solarcaratuva/Batterytester/Firmware/Discharge/Discharge/Discharger.cpp

#include "Discharger.h"
Discharger::Discharger(int MYSELPIN,int MYDATAOUT,int MYDATAIN,int MYSPICLOCK){
	SELPIN = MYSELPIN;
	DATAOUT = MYDATAOUT;
	DATAIN = MYDATAIN;
	SPICLOCK = MYSPICLOCK;	
}

int Discharger::read_adc(int channel){
  int adcvalue = 0;
  byte commandbits = B11000000; //command bits - start, mode, chn (3), dont care (3)
  //allow channel selection
  commandbits|=((channel-1)<<3);
  digitalWrite(SELPIN,LOW); //Select adc
  // setup bits to be written
  for (int i=7; i>=3; i--){
    digitalWrite(DATAOUT,commandbits&1<<i);
    //cycle clock
    digitalWrite(SPICLOCK,HIGH);
    digitalWrite(SPICLOCK,LOW);    
  }
  digitalWrite(SPICLOCK,HIGH);    //ignores 2 null bits
  digitalWrite(SPICLOCK,LOW);
  digitalWrite(SPICLOCK,HIGH);  
  digitalWrite(SPICLOCK,LOW);
  //read bits from adc
  for (int i=11; i>=0; i--){
    adcvalue+=digitalRead(DATAIN)<<i;
    //cycle clock
    digitalWrite(SPICLOCK,HIGH);
    digitalWrite(SPICLOCK,LOW);
  }
  digitalWrite(SELPIN, HIGH); //turn off device
  return adcvalue;
}

void Discharger::initialize(){
  //set pin modes 
  pinMode(SELPIN, OUTPUT); 
  pinMode(DATAOUT, OUTPUT); 
  pinMode(DATAIN, INPUT); 
  pinMode(SPICLOCK, OUTPUT); 
  //disable device to start with 
  digitalWrite(SELPIN,HIGH); 
  digitalWrite(DATAOUT,LOW); 
  digitalWrite(SPICLOCK,LOW); 
}
